Sakati84/3DPrintColorizer/Hardware/PenHolderArm_Ender3v2_byMolesza.stl

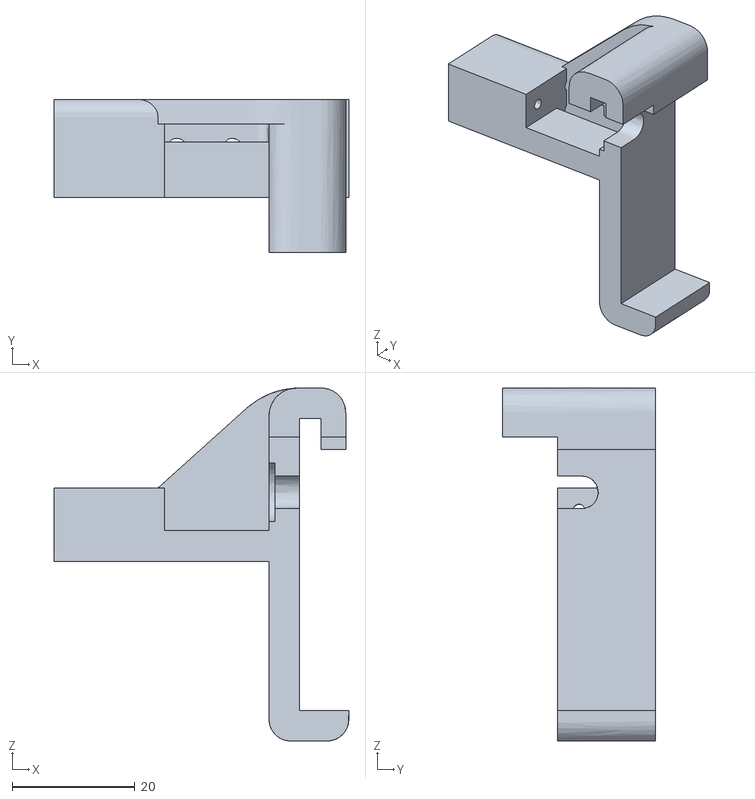
[picture p17: CAD file, 2021-08-01]
Hardware/PenHolderArm_Ender3v2_byMolesza.stl
48.0 x 25.0 x 57.5
