Sakati84/3DPrintColorizer/Hardware/BLTouchPenHolder/PenHolder_Long+4.stl

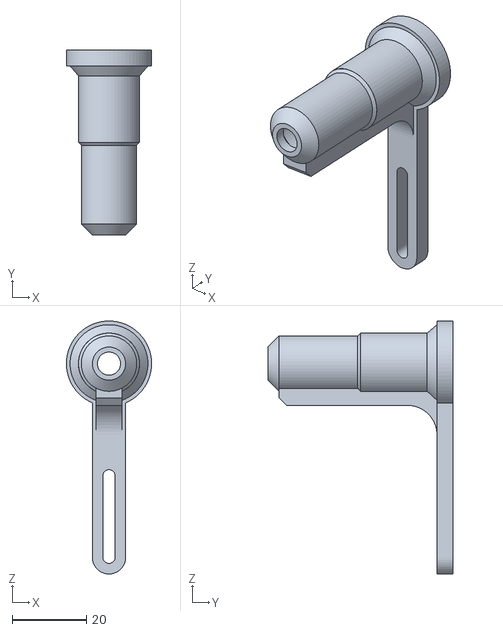
[picture p18: CAD file, 2021-08-01]
Hardware/BLTouchPenHolder/PenHolder_Long+4.stl
23.0 x 50.0 x 68.2
