Sakati84/3DPrintColorizer/Hardware/PenHolder_Sharpie.stl

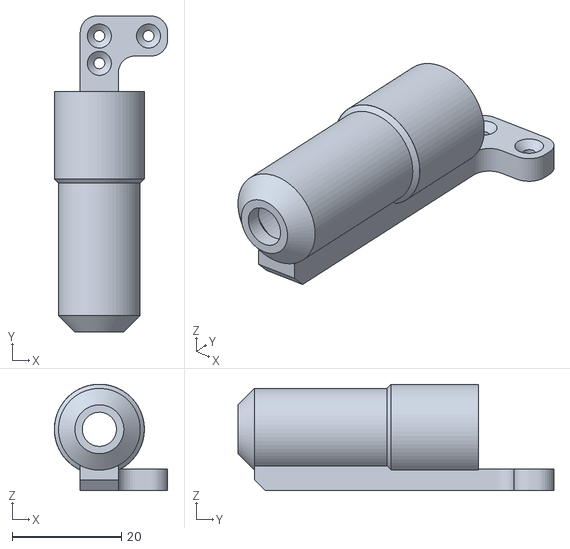
[picture p19: CAD file, 2021-07-19]
Hardware/PenHolder_Sharpie.stl
20.7 x 57.8 x 19.5
