Sakati84/3DPrintColorizer/Hardware/BLTouchPenHolder/PenHolder_Long+3.stl

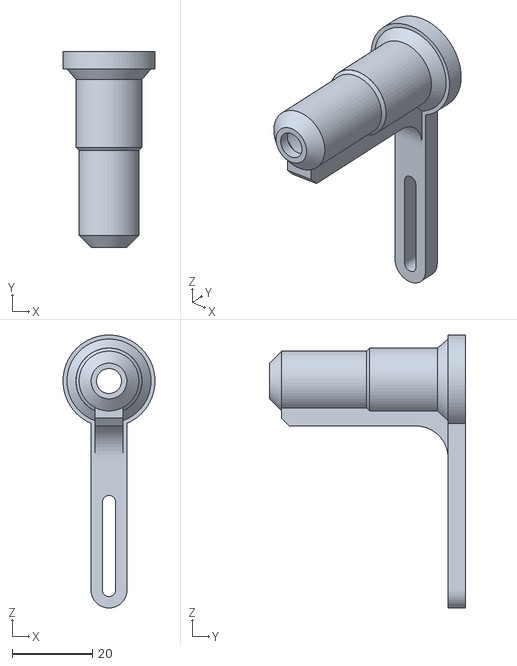
[picture p20: CAD file, 2021-08-01]
Hardware/BLTouchPenHolder/PenHolder_Long+3.stl
23.0 x 49.0 x 68.2
