Sakati84/3DPrintColorizer/Hardware/PenCap.stl

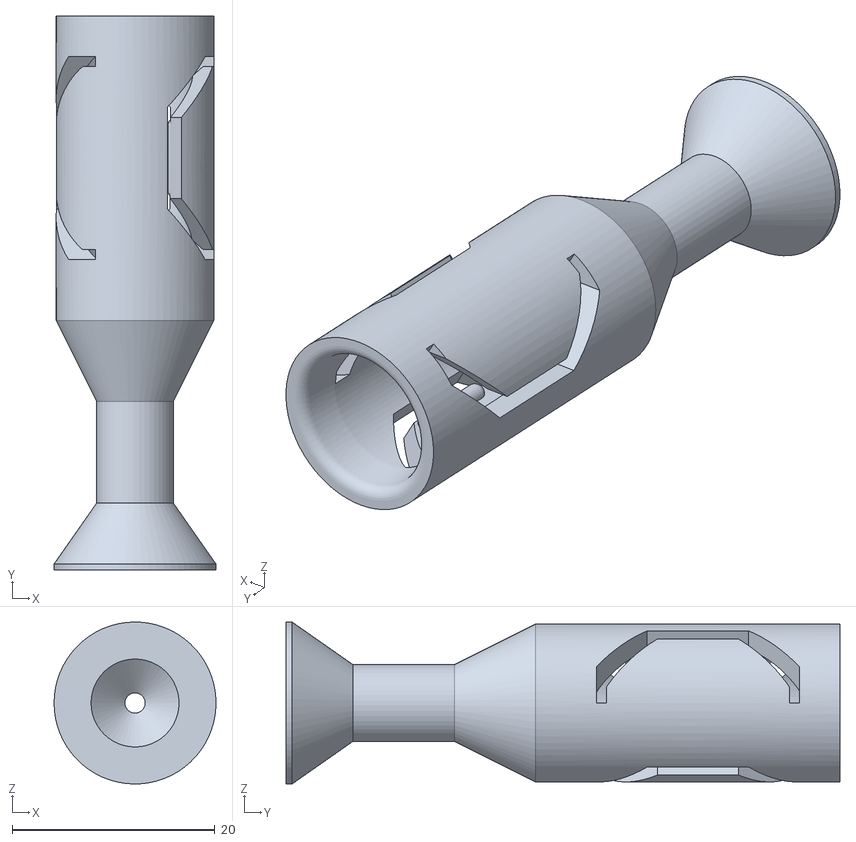
[picture p21: CAD file, 2021-07-19]
Hardware/PenCap.stl
16.0 x 54.6 x 16.0
