Sakati84/3DPrintColorizer/Hardware/BLTouchPenHolder/PenHolder_Short.stl

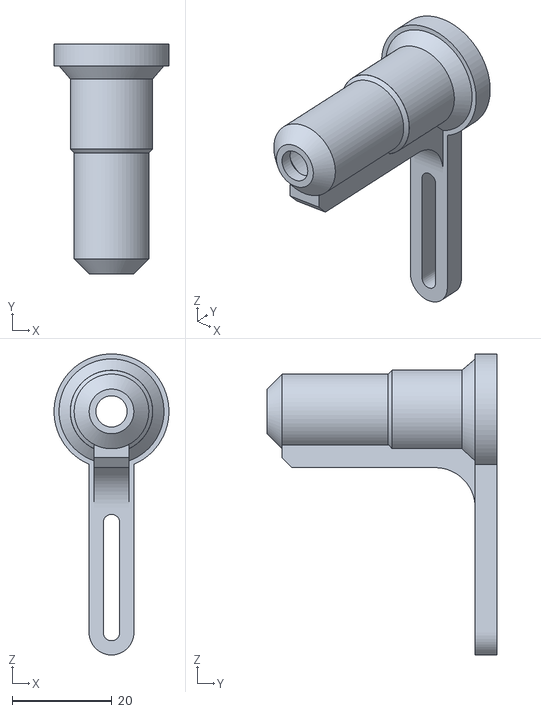
[picture p22: CAD file, 2021-08-01]
Hardware/BLTouchPenHolder/PenHolder_Short.stl
23.0 x 46.0 x 60.2
