Sakati84/3DPrintColorizer/Hardware/PenHolder_Amazon_ShuttleArt(_Sharpie).stl

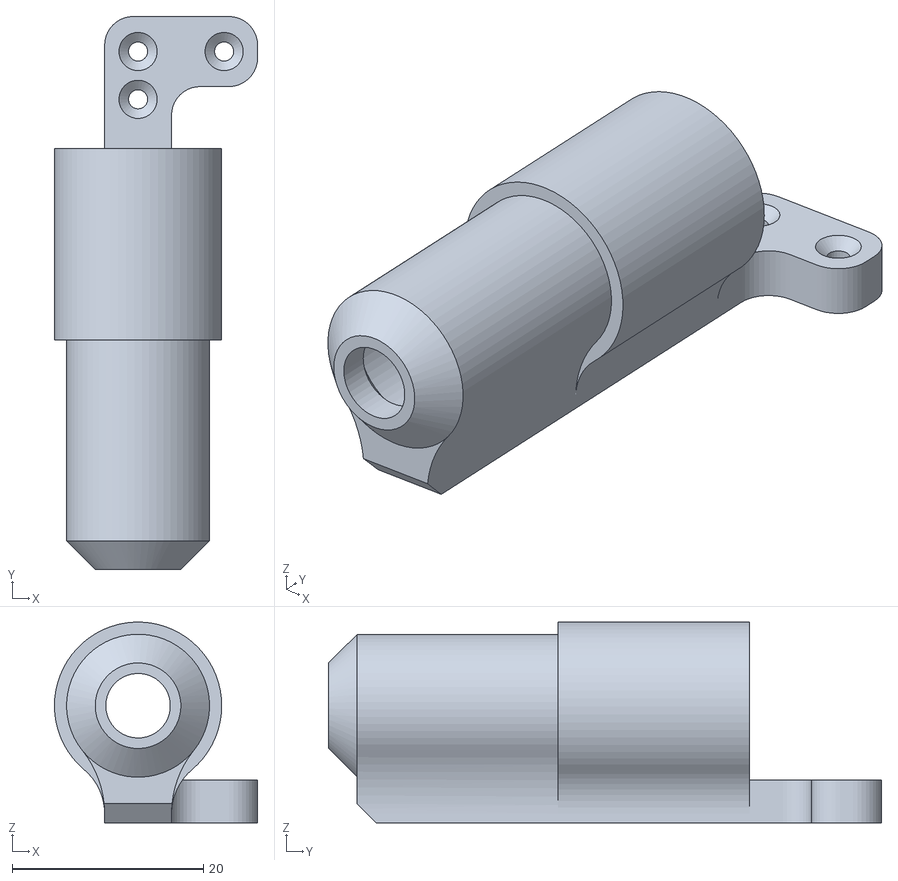
[picture p23: CAD file, 2021-07-19]
Hardware/PenHolder_Amazon_ShuttleArt(_Sharpie).stl
21.2 x 57.8 x 21.0
