Sakati84/3DPrintColorizer/Hardware/BLTouchPenHolder/PenHolder_Long.stl

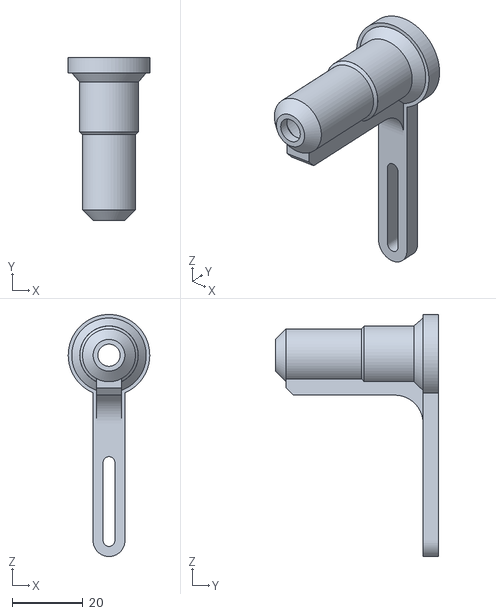
[picture p24: CAD file, 2021-08-01]
Hardware/BLTouchPenHolder/PenHolder_Long.stl
23.0 x 46.0 x 68.2
