Sakati84/3DPrintColorizer/Hardware/PenHolderArm_Ender3v1.stl

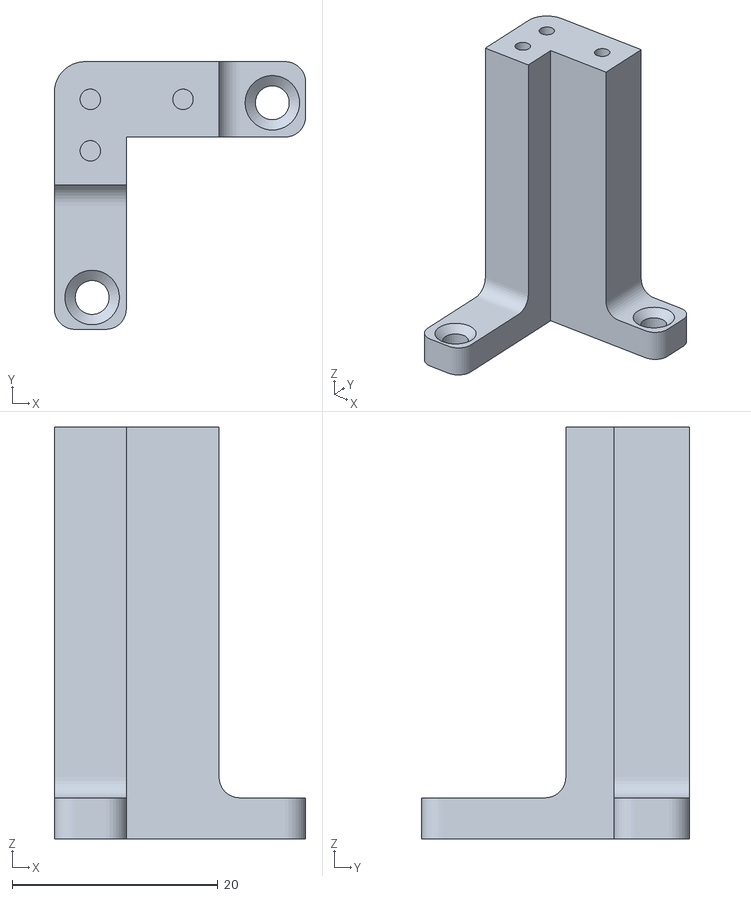
[picture p25: CAD file, 2021-07-19]
Hardware/PenHolderArm_Ender3v1.stl
24.4 x 26.0 x 40.0
