Sakati84/3DPrintColorizer/Hardware/BLTouchPenHolder/PenHolder_Long+5.stl

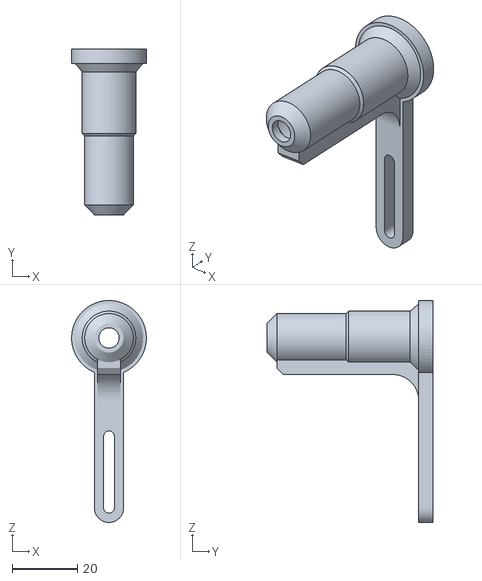
[picture p26: CAD file, 2021-08-01]
Hardware/BLTouchPenHolder/PenHolder_Long+5.stl
23.0 x 51.0 x 68.2
