Sakati84/3DPrintColorizer/Hardware/BLTouchPenHolder/PenHolder_Short+4.stl

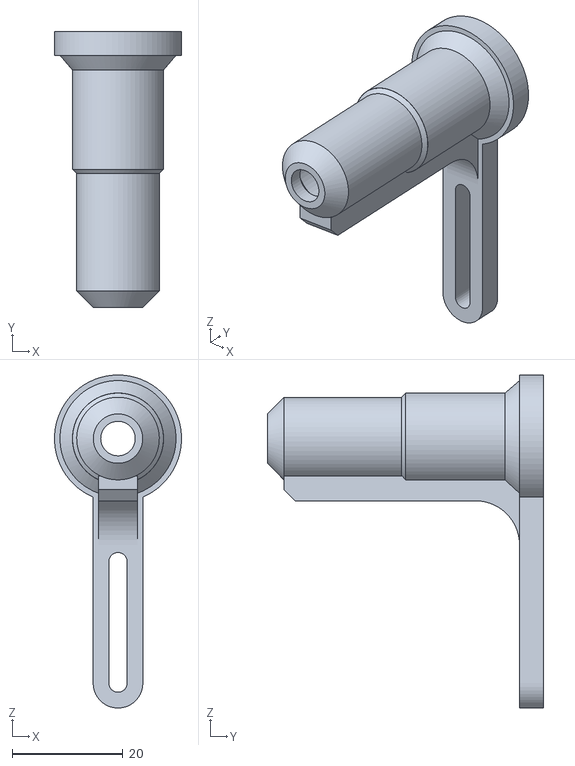
[picture p27: CAD file, 2021-08-01]
Hardware/BLTouchPenHolder/PenHolder_Short+4.stl
23.0 x 50.0 x 60.2
