Sakati84/3DPrintColorizer/Hardware/BLTouchPenHolder/PenHolder_Short+2.stl

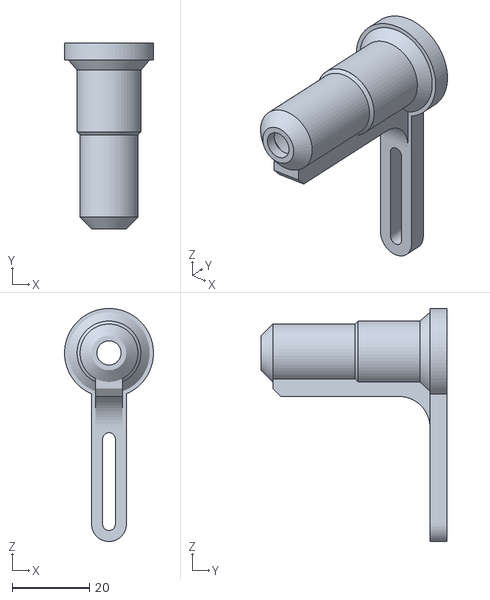
[picture p28: CAD file, 2021-08-01]
Hardware/BLTouchPenHolder/PenHolder_Short+2.stl
23.0 x 48.0 x 60.2
